parya7254/AtmosCore/Journals/images/battery-charger.png

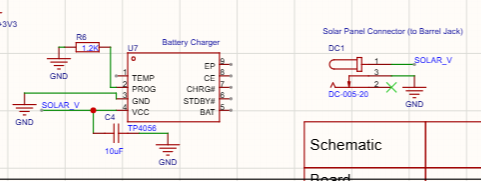
Journals/images/battery-charger.png
